menehune23/arduboy-dotmg/assets/advance_front.png

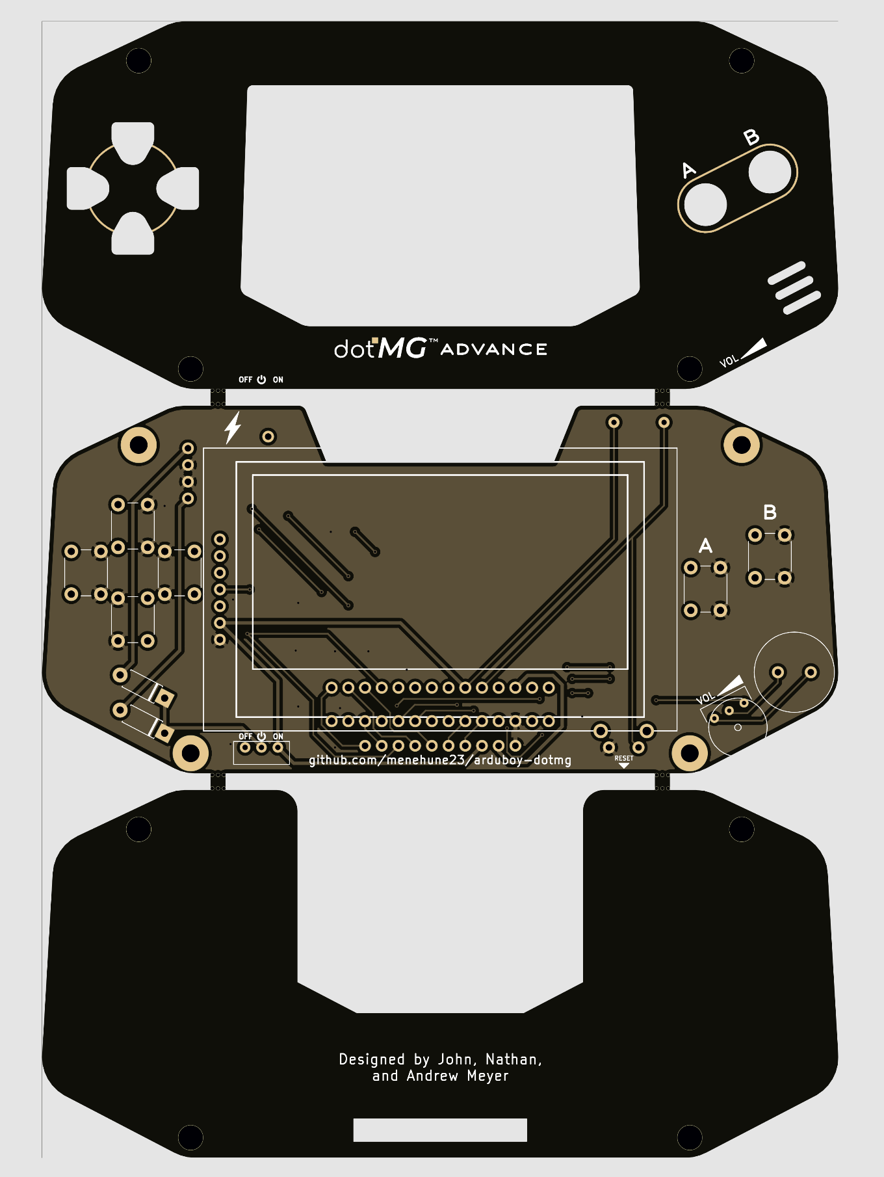
assets/advance_front.png
