menehune23/arduboy-dotmg/assets/cart_back.png

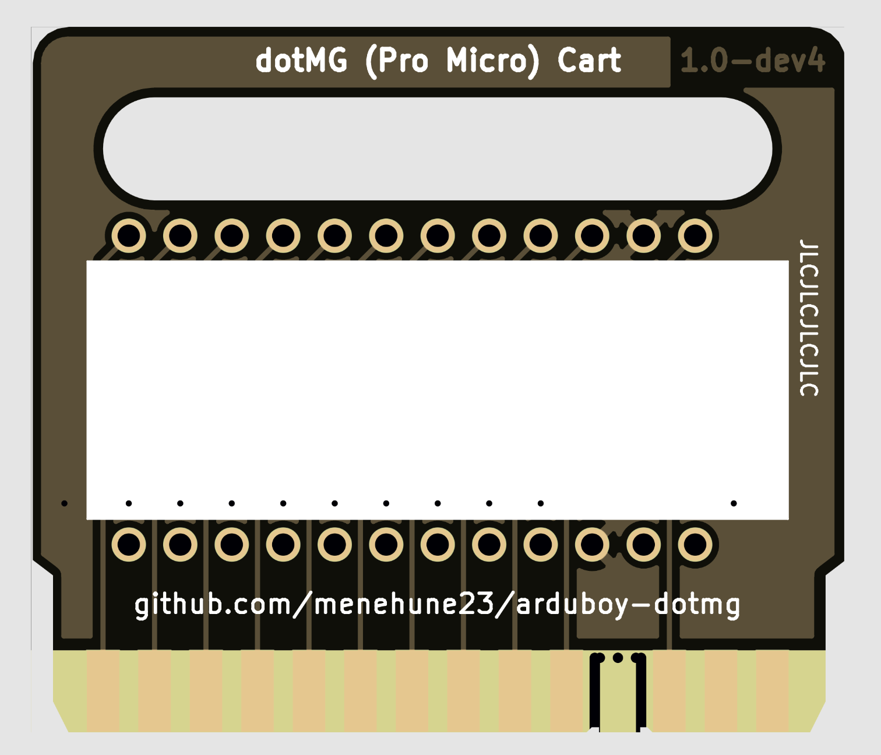
assets/cart_back.png
