menehune23/arduboy-dotmg/assets/cart_front.png

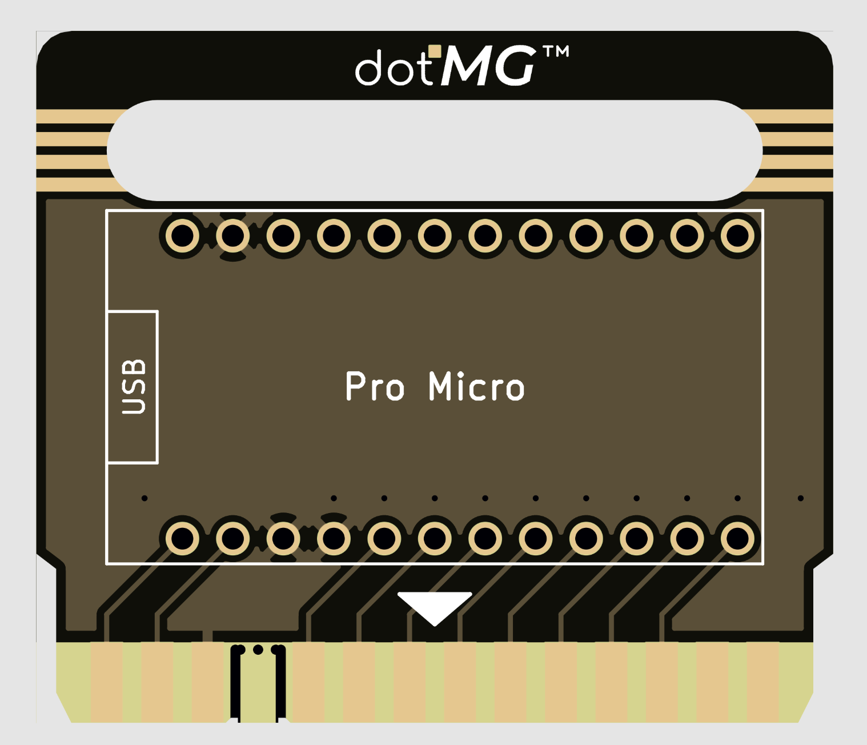
assets/cart_front.png
