menehune23/arduboy-dotmg/assets/dotmg.png

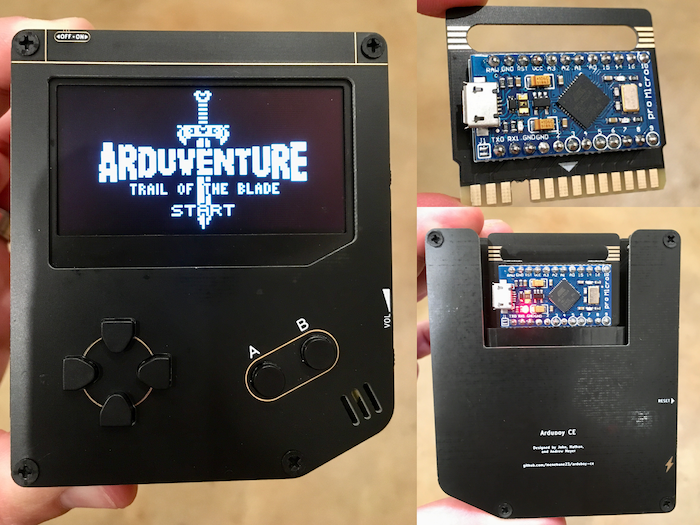
assets/dotmg.png
