menehune23/arduboy-dotmg/assets/front_black.png

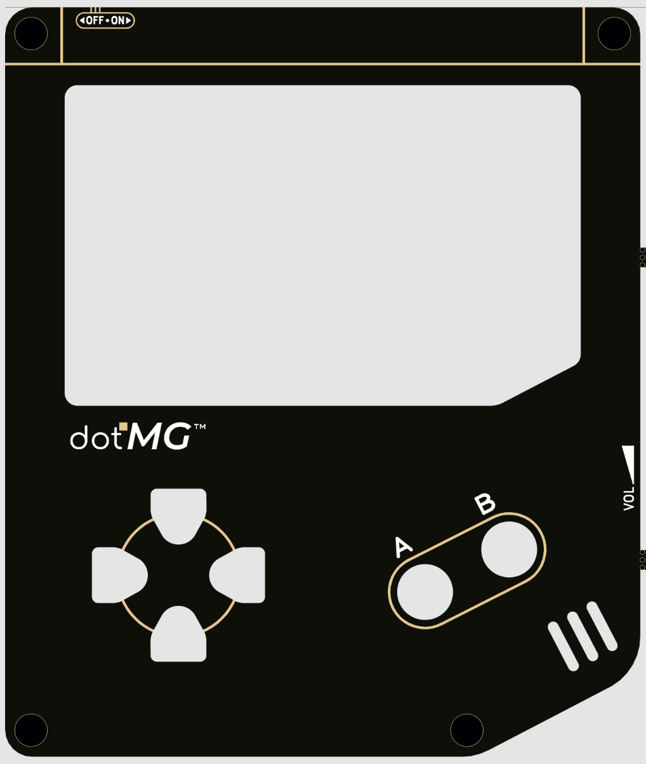
assets/front_black.png
