menehune23/arduboy-dotmg/assets/front_white.png

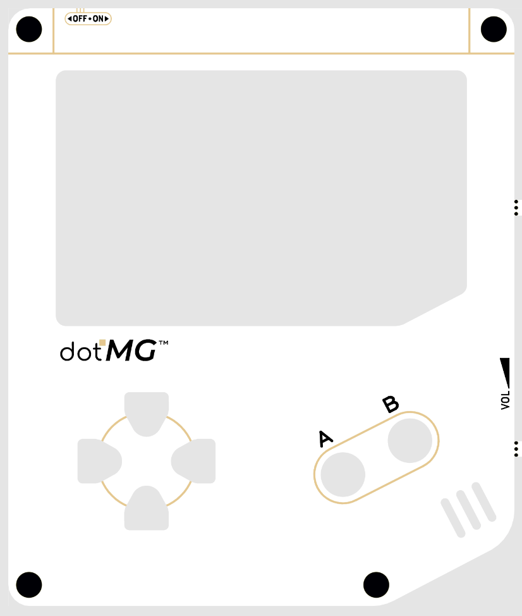
assets/front_white.png
